nhhxhln/Agent-Indicator/tools/ui_sim/shots/ui-devices.bmp

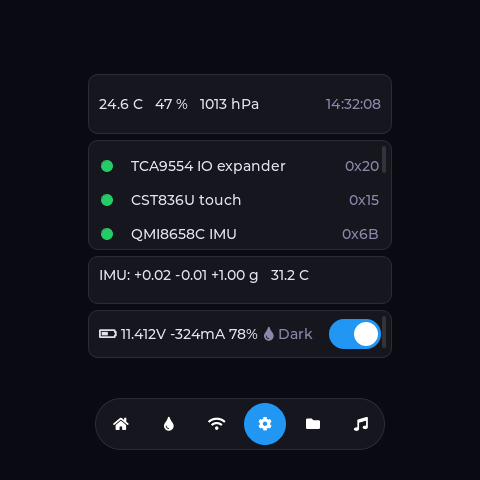
tools/ui_sim/shots/ui-devices.bmp
