nhhxhln/Agent-Indicator/tools/ui_sim/shots/ui-files.bmp

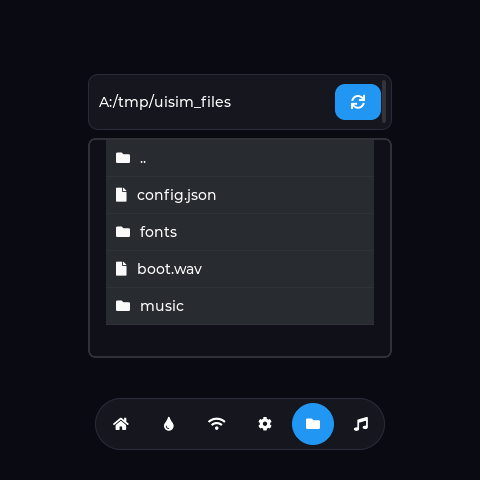
tools/ui_sim/shots/ui-files.bmp
