nhhxhln/Agent-Indicator/tools/ui_sim/shots/ui-light-files.bmp

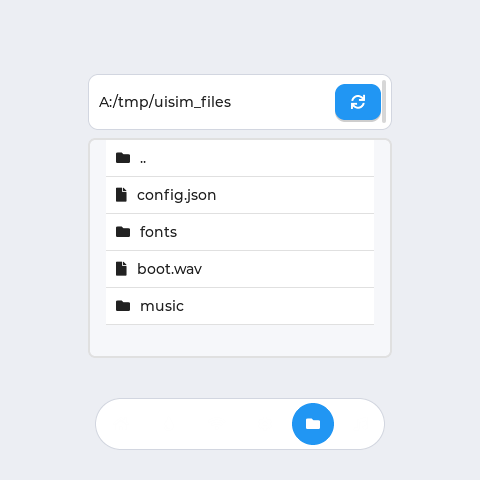
tools/ui_sim/shots/ui-light-files.bmp
