nhhxhln/Agent-Indicator/tools/ui_sim/shots/ui-light-music.bmp

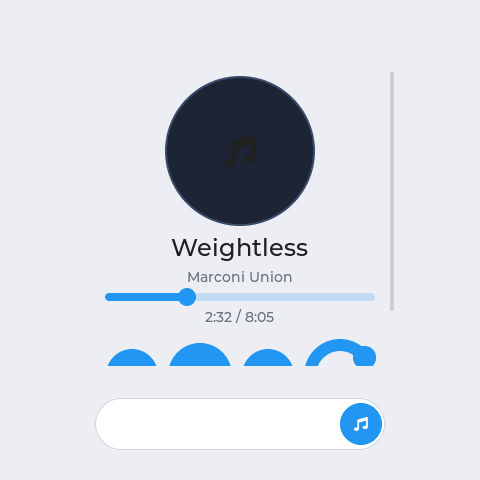
tools/ui_sim/shots/ui-light-music.bmp
