nhhxhln/Agent-Indicator/tools/ui_sim/shots/ui-light-wifi.bmp

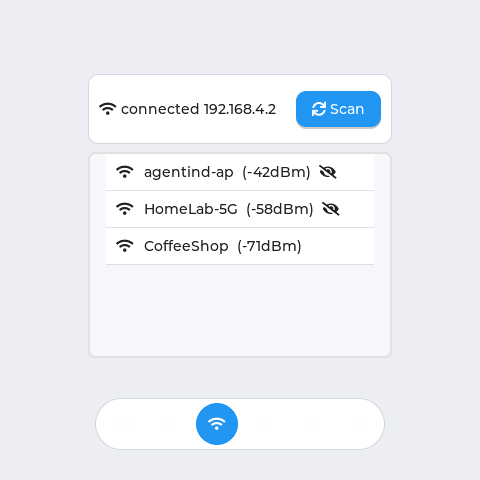
tools/ui_sim/shots/ui-light-wifi.bmp
