nhhxhln/Agent-Indicator/tools/ui_sim/shots/ui-wifi.bmp

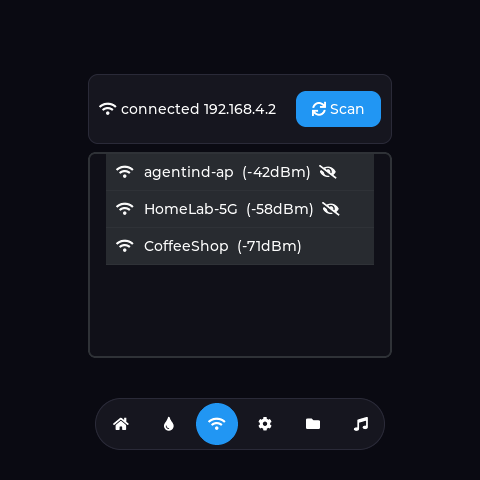
tools/ui_sim/shots/ui-wifi.bmp
